seperool/Pinball_Arduino/RMarkdown/Imagens/Estrutura_ortogonal.jpeg

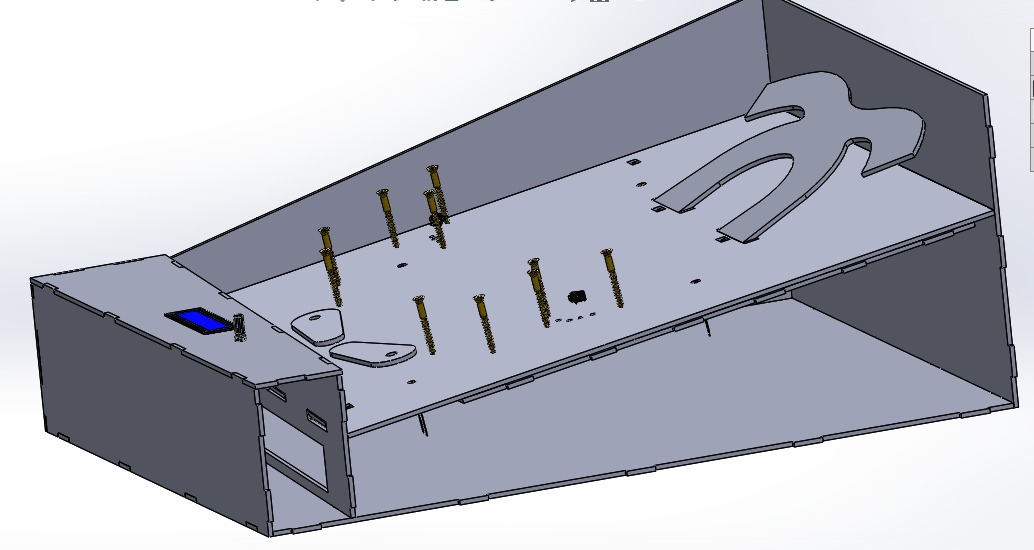
RMarkdown/Imagens/Estrutura_ortogonal.jpeg
